TinyCircuits/TinyCircuits-TinyShield-Gyro-ASD2614/examples/TinyShield_Gyro/LICENSE.h

The MIT License (MIT)

Copyright (c) 2014 Samwell Freeman

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
